phuonglvh/Long-Distance-Transportation-Monitoring-System/Doc/img/5.png

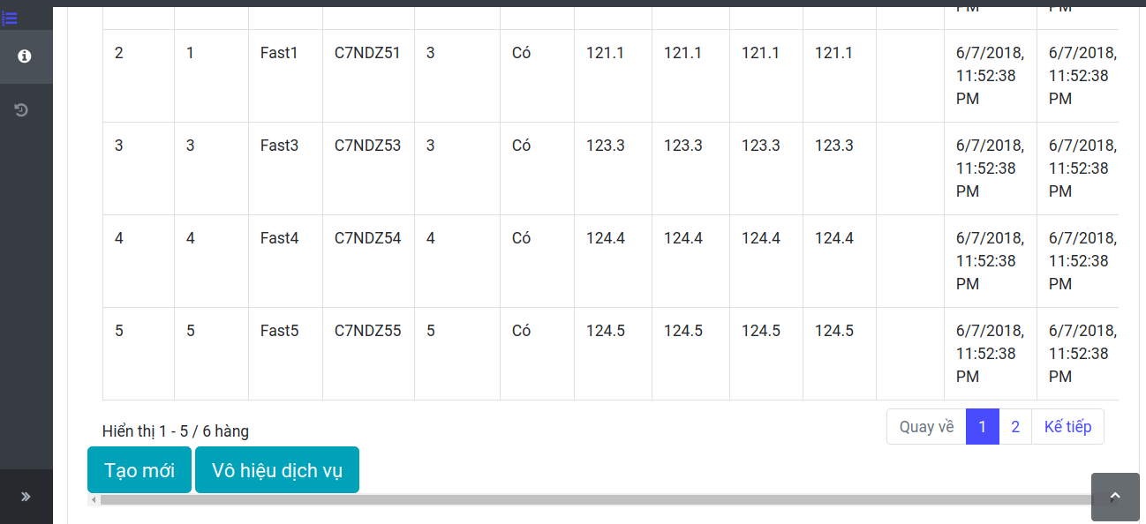
Doc/img/5.png
